hpsaturn/quadpod/docs/Blue stepdown up.jpg

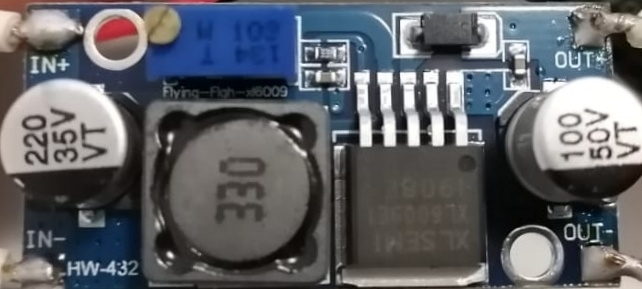
docs/Blue stepdown up.jpg
