hpsaturn/quadpod/docs/mini stepdown.jpg

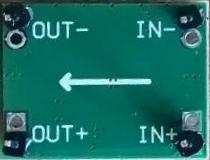
docs/mini stepdown.jpg
