hpsaturn/quadpod/images/Aragog v34a.png

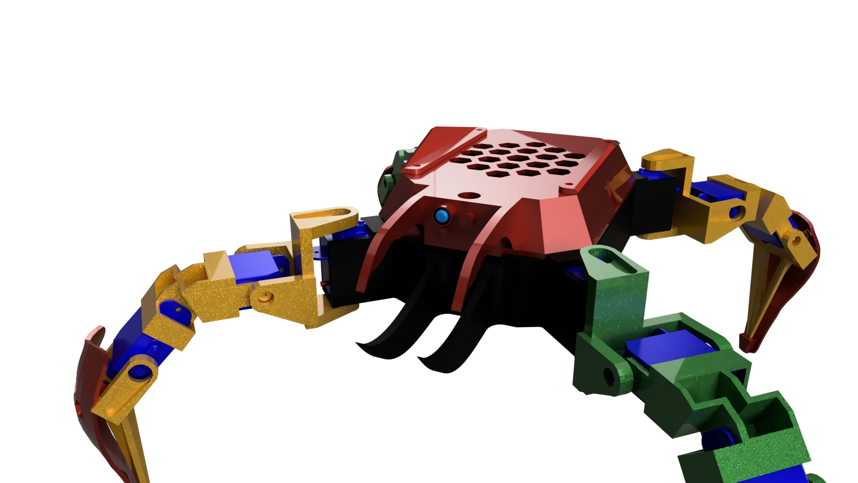
images/Aragog v34a.png
