hpsaturn/quadpod/images/Aragog v34b.png

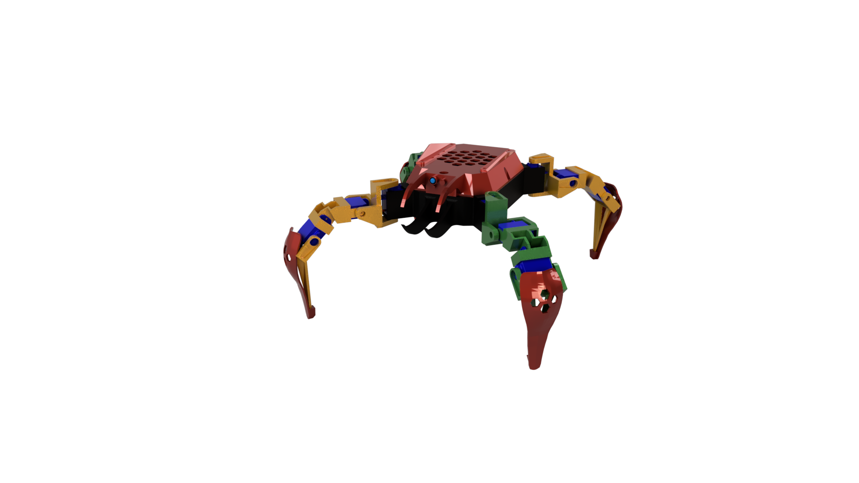
images/Aragog v34b.png
